jb-flamant/trackball/comparaison_embase.png

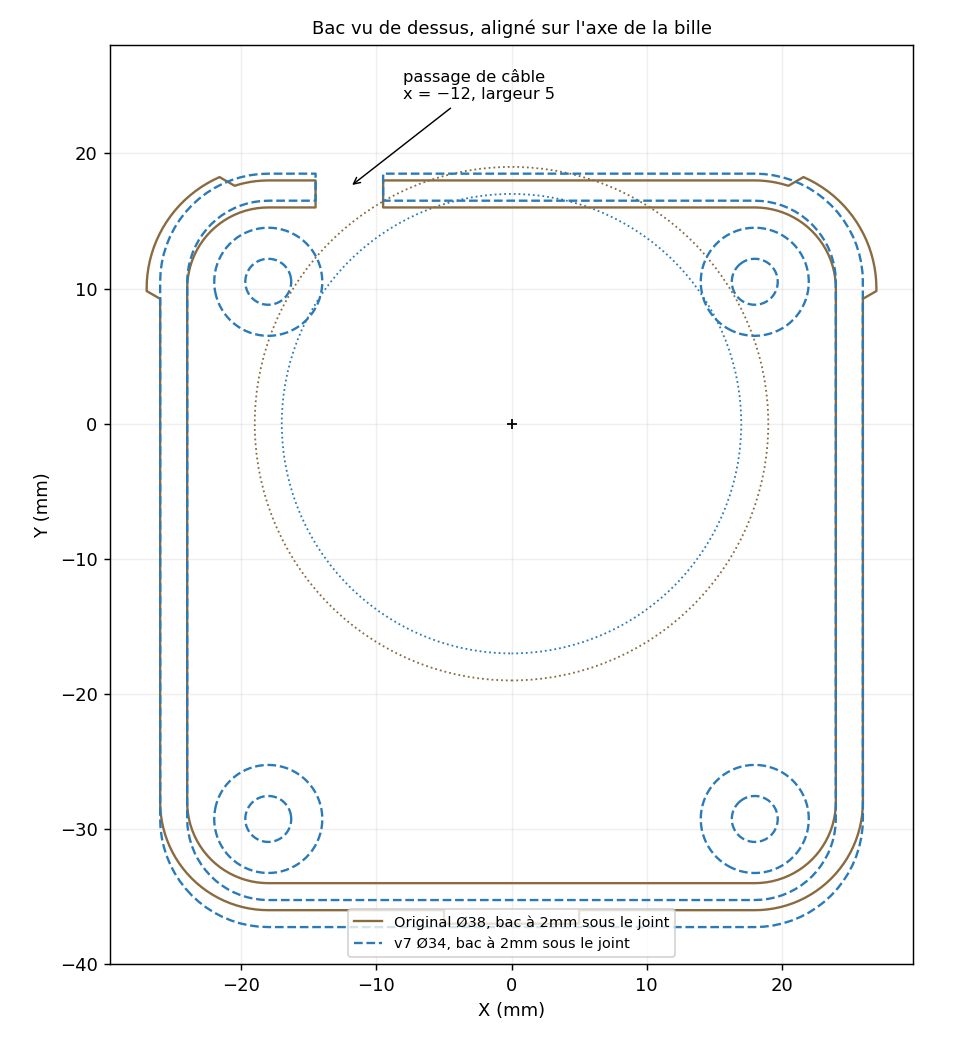
comparaison_embase.png
