jb-flamant/trackball/detail_levre.png

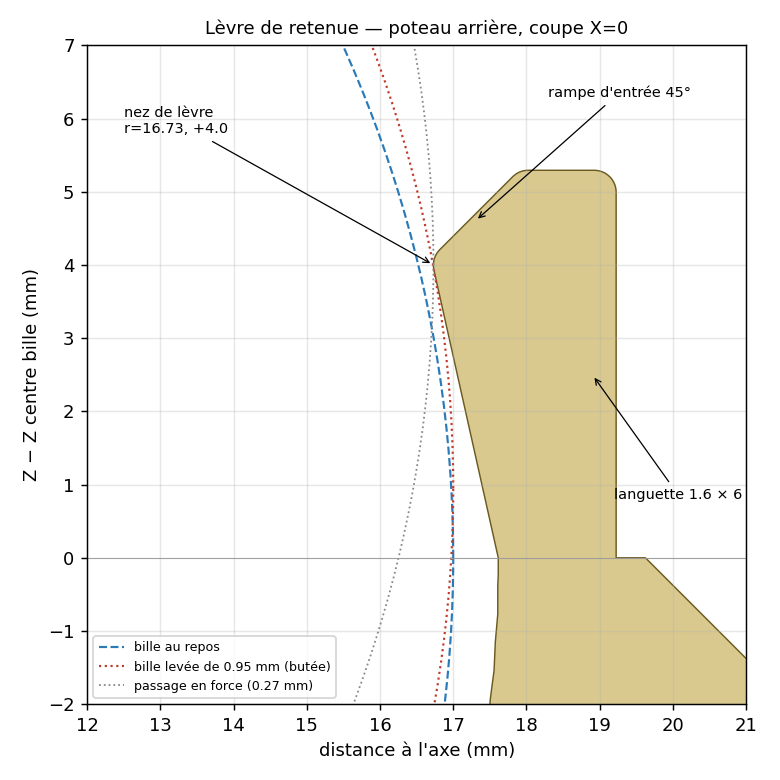
detail_levre.png
