jb-flamant/trackball/iso.png

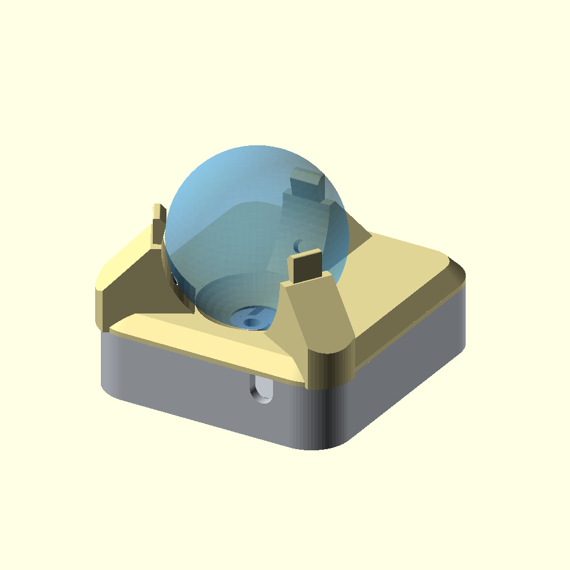
iso.png
