jb-flamant/trackball/passage_cable.png

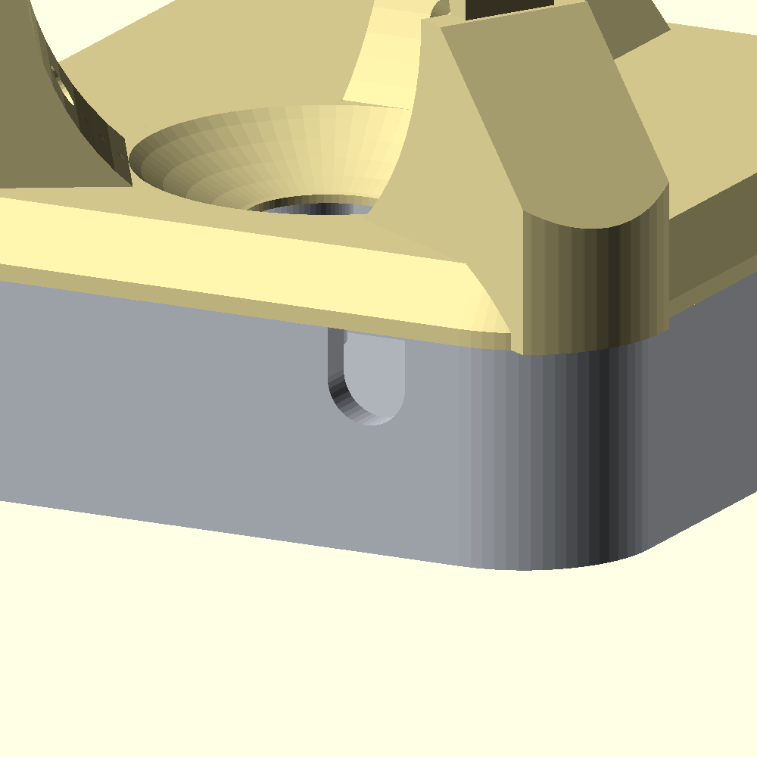
passage_cable.png
