jb-flamant/trackball/section_horizontale.png

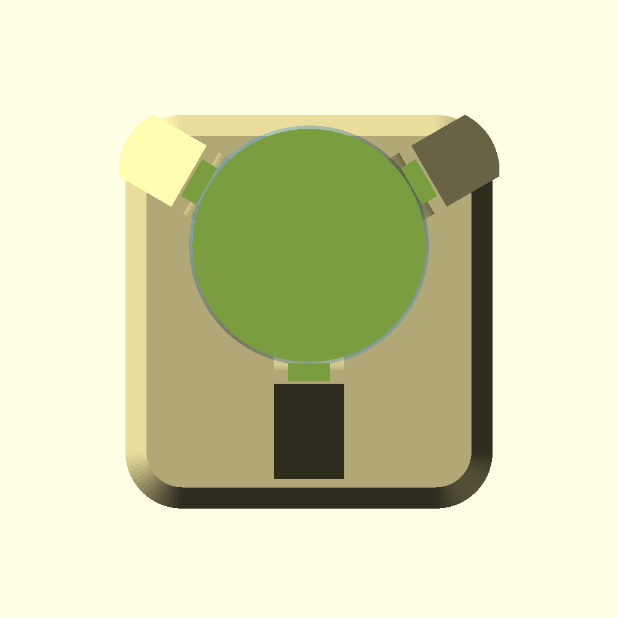
section_horizontale.png
