jb-flamant/trackball/view_bas.png

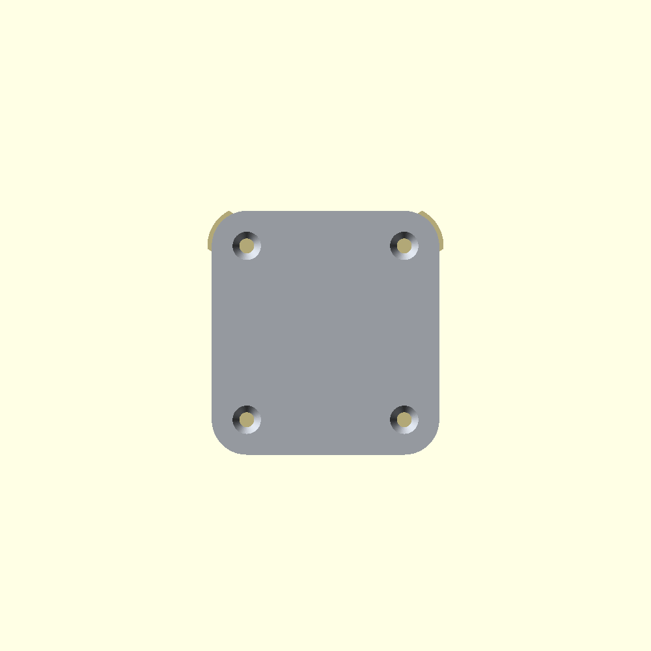
view_bas.png
